felhub/spark_calibrator/simulation/spark_calibrator.asc

C1: cap; .47µ
D1: diode; gl34g
D2: diode; gl34g
L1: ind; 8m; Ipk=10 Rser=1
R1: res; 2.2k
R2: res; 2.2k
R3: res; 330
U1: 4N28
U2: BS170
U3: irfp460
V1: voltage; 12
V2: voltage; PULSE(0 5 2m 2u 2u 4m 8m)
Named nets: 0
.tran 8m
